MSMGreen/at-departure-board/tests/golden/check_config.png

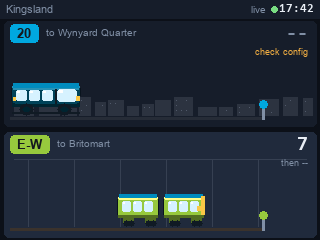
tests/golden/check_config.png
