MSMGreen/at-departure-board/tests/golden/empty.png

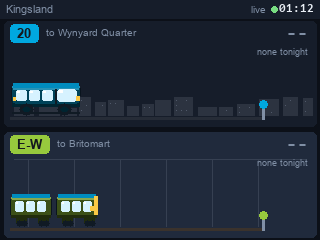
tests/golden/empty.png
