MSMGreen/at-departure-board/tests/golden/four_up.png

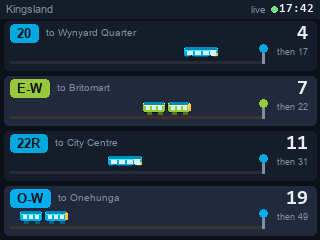
tests/golden/four_up.png
